snchz46/NV-Sensor-Optical-Readout-TIA/data/tia_rf_cf_sweep/results_placeholder.csv

rf_ohms | cf_farads | cutoff_hz
1000000 | 3.3e-12 | 48000
